NaskoEquationersson/rubiks-cube-timer/newer_circuit.jpeg

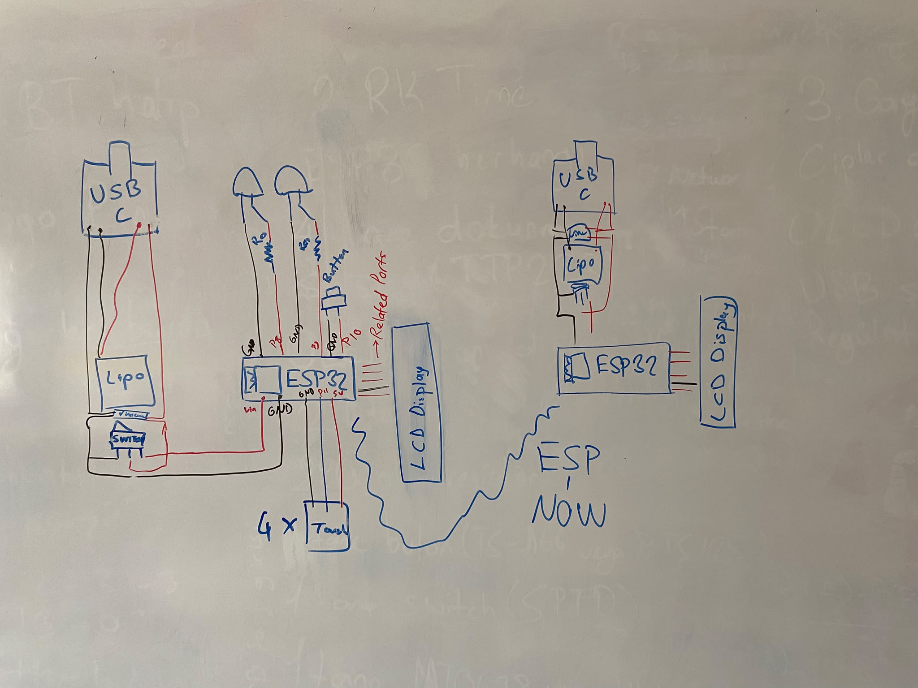
newer_circuit.jpeg
