NaskoEquationersson/rubiks-cube-timer/images/R.png

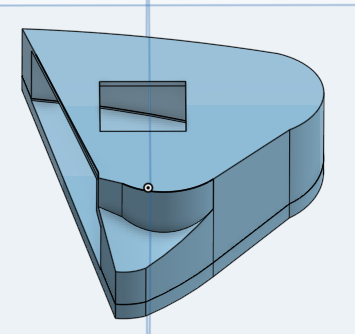
images/R.png
