NaskoEquationersson/rubiks-cube-timer/models_used_for_scale/5mm-led-green-1.snapshot.1/5mm_LED_Green.png

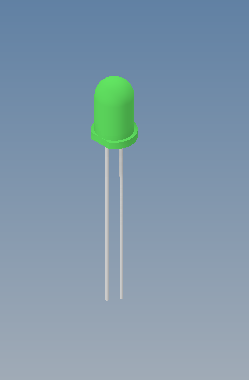
models_used_for_scale/5mm-led-green-1.snapshot.1/5mm_LED_Green.png
