NaskoEquationersson/rubiks-cube-timer/models_used_for_scale/5mm-led-red-2.snapshot.1/5mm_LED_Red.png

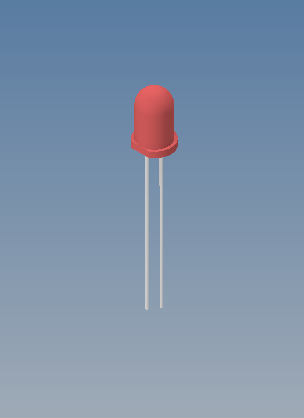
models_used_for_scale/5mm-led-red-2.snapshot.1/5mm_LED_Red.png
