NaskoEquationersson/rubiks-cube-timer/models_used_for_scale/arduino-character-1602-16x2-lcd-display-module-i2c-3-3v-or-5v-1.snapshot.5/3.3V-5V LCD Module 16x2 1602 Character Display,Black on White.jpg

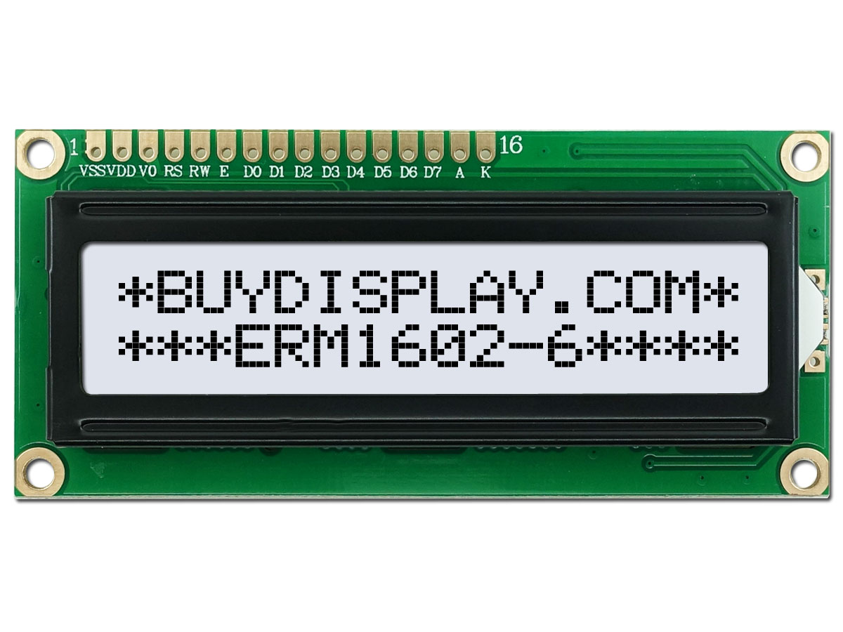
models_used_for_scale/arduino-character-1602-16x2-lcd-display-module-i2c-3-3v-or-5v-1.snapshot.5/3.3V-5V LCD Module 16x2 1602 Character Display,Black on White.jpg
