NaskoEquationersson/rubiks-cube-timer/models_used_for_scale/generic-1-2w-axial-resistor-1.snapshot.1/1_2W_Axial_Res.png

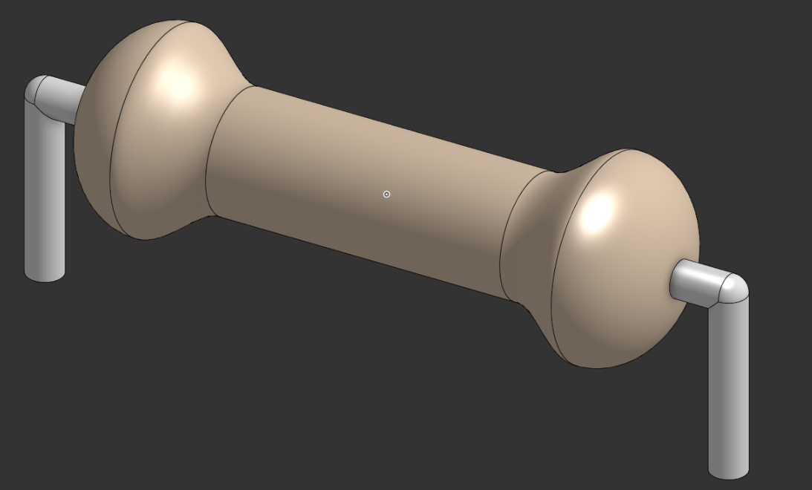
models_used_for_scale/generic-1-2w-axial-resistor-1.snapshot.1/1_2W_Axial_Res.png
