NaskoEquationersson/rubiks-cube-timer/models_used_for_scale/kcd1-on-off-rocker-switch-2-pins-1.snapshot.5/kcd1_view_1.jpg

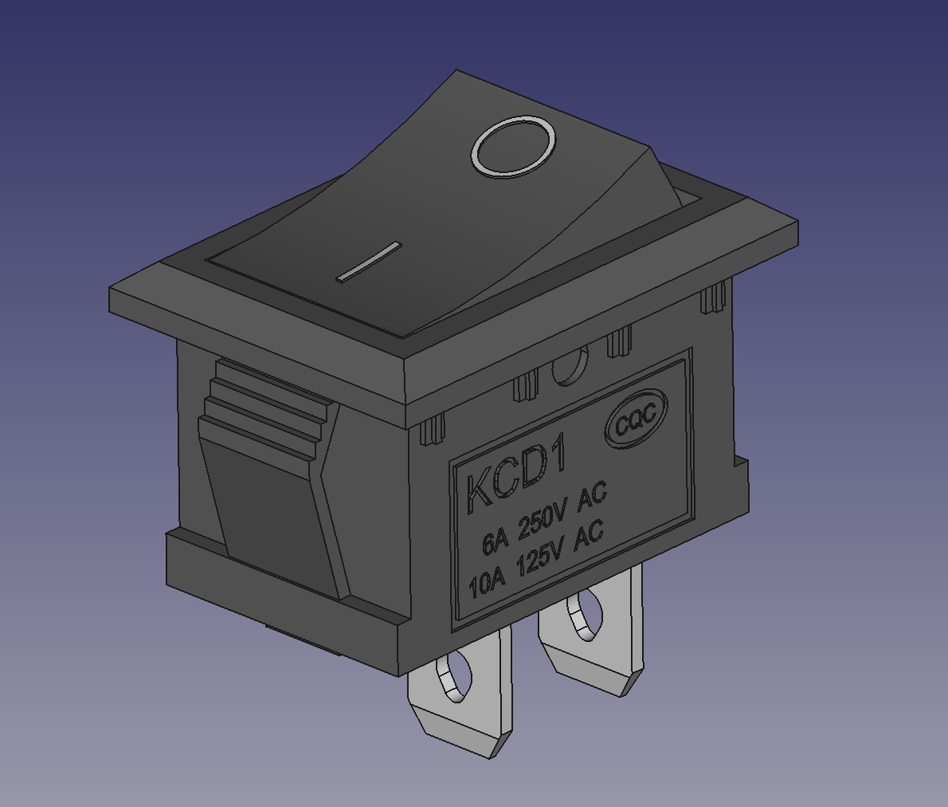
models_used_for_scale/kcd1-on-off-rocker-switch-2-pins-1.snapshot.5/kcd1_view_1.jpg
