NaskoEquationersson/rubiks-cube-timer/models_used_for_scale/layout-1.jpeg

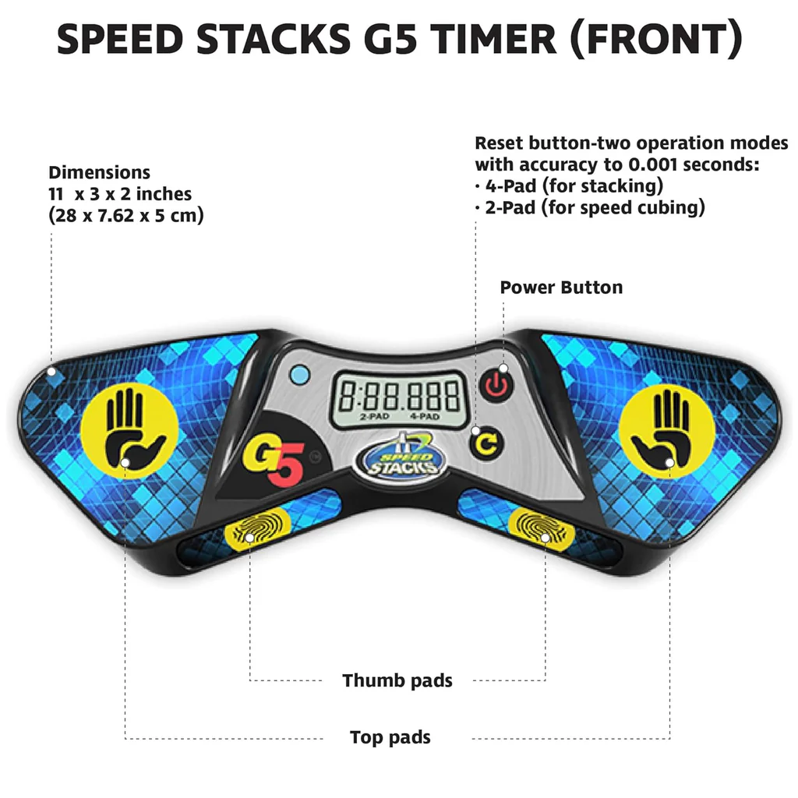
models_used_for_scale/layout-1.jpeg
