NaskoEquationersson/rubiks-cube-timer/models_used_for_scale/layout-2.jpeg

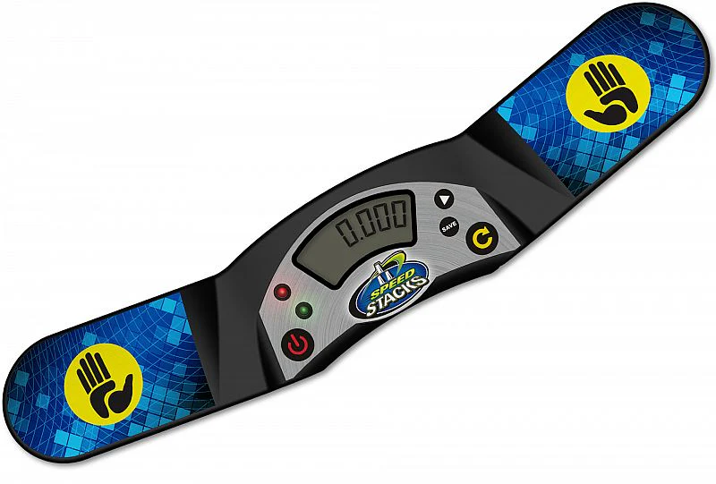
models_used_for_scale/layout-2.jpeg
