NaskoEquationersson/rubiks-cube-timer/models_used_for_scale/micro-momentary-tactile-tact-touch-push-button-switch-6x6x6-mm-1.snapshot.4/Micro Momentary Tactile Tact Touch Push Button Switch, 6x6x6 mm v3.png

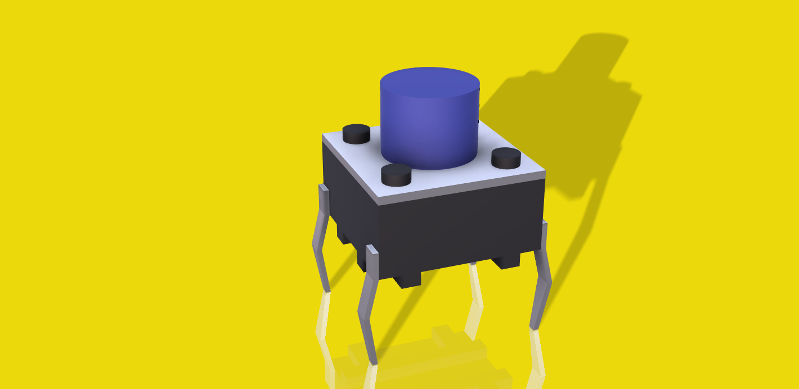
models_used_for_scale/micro-momentary-tactile-tact-touch-push-button-switch-6x6x6-mm-1.snapshot.4/Micro Momentary Tactile Tact Touch Push Button Switch, 6x6x6 mm v3.png
