NaskoEquationersson/rubiks-cube-timer/models_used_for_scale/square-push-button-ds-431-1.snapshot.13/Square Push Button DS-431 Preview 5.jpg

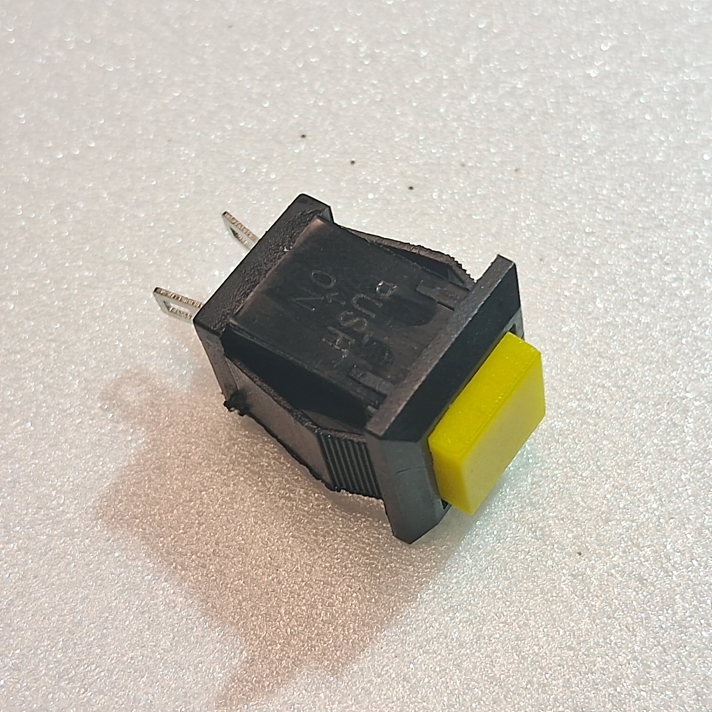
models_used_for_scale/square-push-button-ds-431-1.snapshot.13/Square Push Button DS-431 Preview 5.jpg
