NaskoEquationersson/rubiks-cube-timer/models_used_for_scale/tp4056-mini-type-c-battery-charging-module-1.snapshot.1/TP4056 mini_2.png

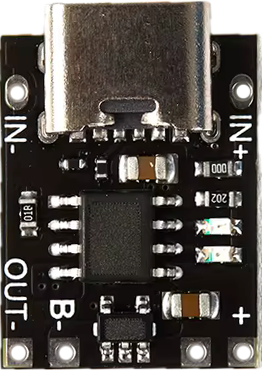
models_used_for_scale/tp4056-mini-type-c-battery-charging-module-1.snapshot.1/TP4056 mini_2.png
